mztejero/BLE_Remote_Control/BLE_Remote_Control/main/buttons.c

#include "config.h"

#include <stdio.h>
#include "freertos/FreeRTOS.h"

// Read Pins
void read_pins(void) {

    int sw_el = gpio_get_level(pins.sw_enc_l);
    int sw_er = gpio_get_level(pins.sw_enc_r);
    int sw_jl = gpio_get_level(pins.sw_js_l);
    int sw_jr = gpio_get_level(pins.sw_js_r);
}
